k33bz/govee-outdoor-pegboard/models/cord_clips/cord_staple_13mm.stl

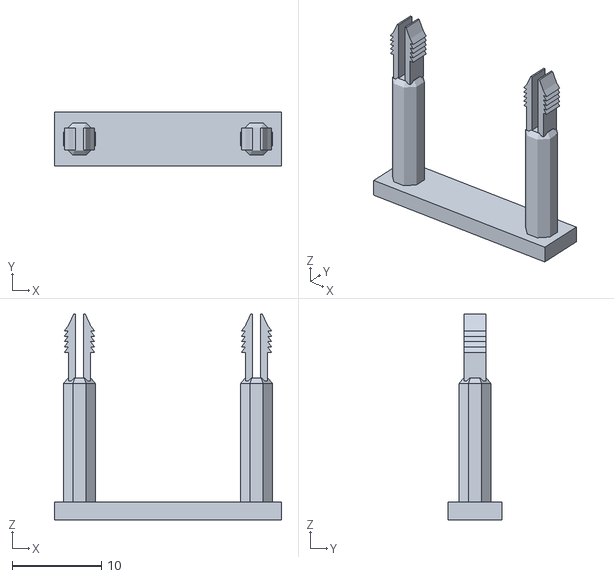
[picture p15: CAD file, 2026-08-23]
models/cord_clips/cord_staple_13mm.stl
25.5 x 6.00 x 23.1
