k33bz/govee-outdoor-pegboard/models/strip_mount/pitchspan_4.98mm.stl

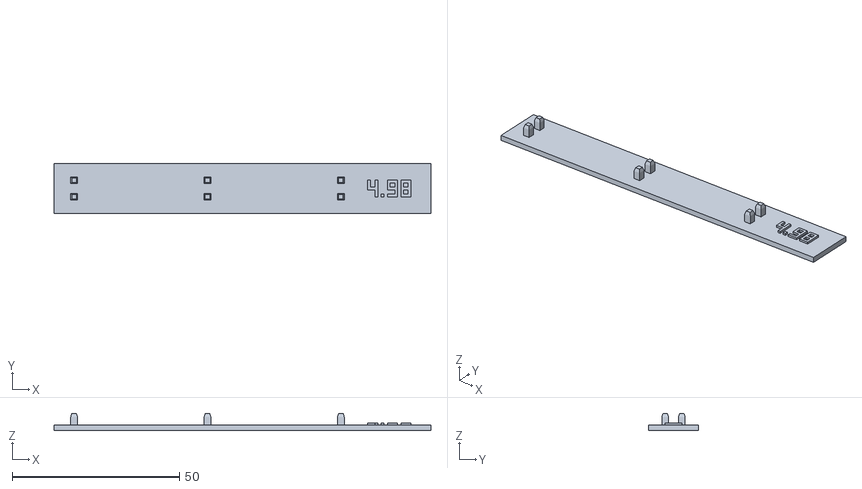
[picture p16: CAD file, 2026-08-21]
models/strip_mount/pitchspan_4.98mm.stl
112.6 x 15.0 x 5.10
