k33bz/govee-outdoor-pegboard/models/cord_clips/cord_staple_04mm.stl

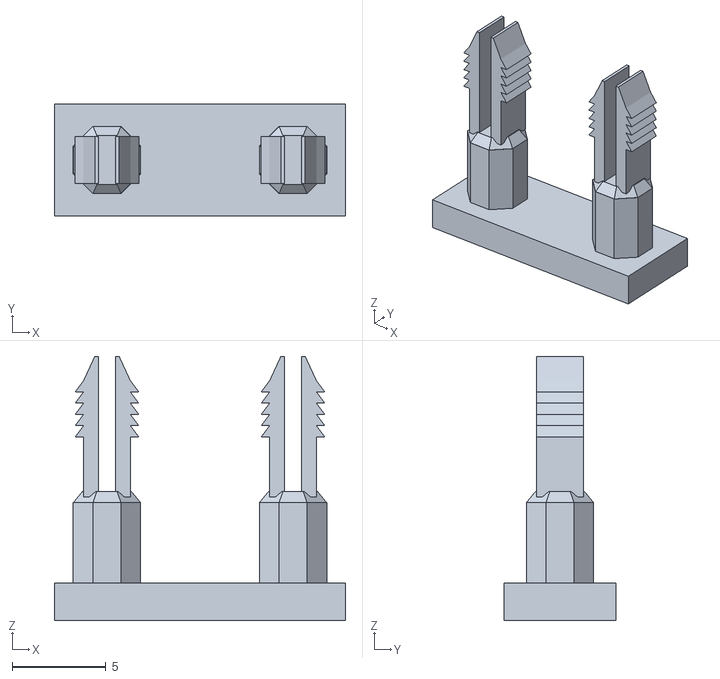
[picture p17: CAD file, 2026-08-23]
models/cord_clips/cord_staple_04mm.stl
15.5 x 6.00 x 14.1
