k33bz/govee-outdoor-pegboard/models/test_gauges/peg_size_gauge.stl

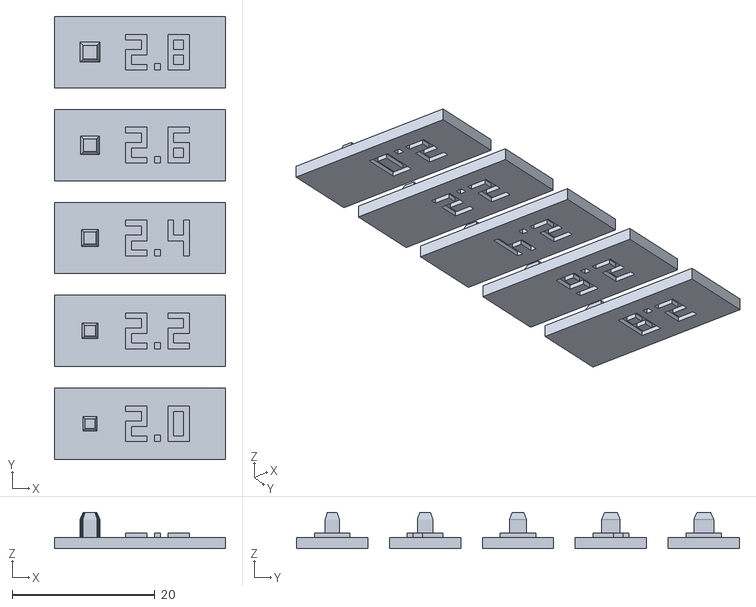
[picture p18: CAD file, 2026-08-20]
models/test_gauges/peg_size_gauge.stl
24.0 x 62.0 x 5.10
