k33bz/govee-outdoor-pegboard/models/cord_clips/cord_arch_10mm.stl

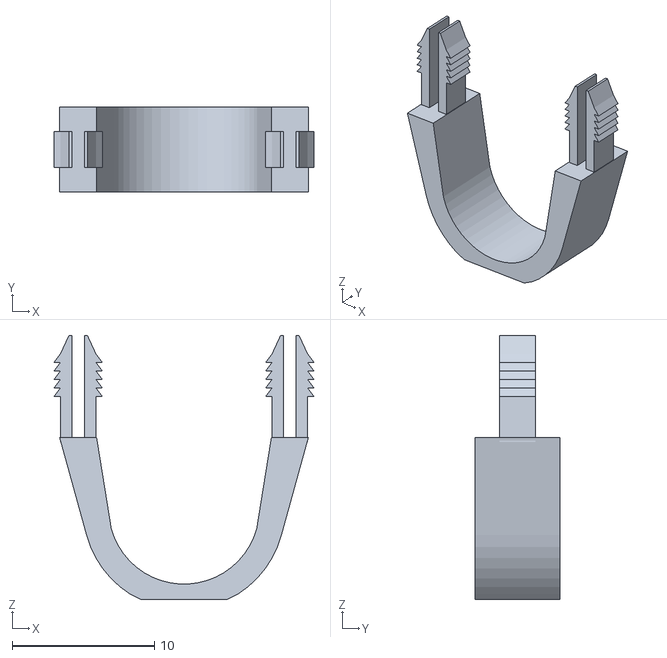
[picture p19: CAD file, 2026-08-23]
models/cord_clips/cord_arch_10mm.stl
18.3 x 6.00 x 18.6
