k33bz/govee-outdoor-pegboard/models/cord_clips/cord_arch_06mm.stl

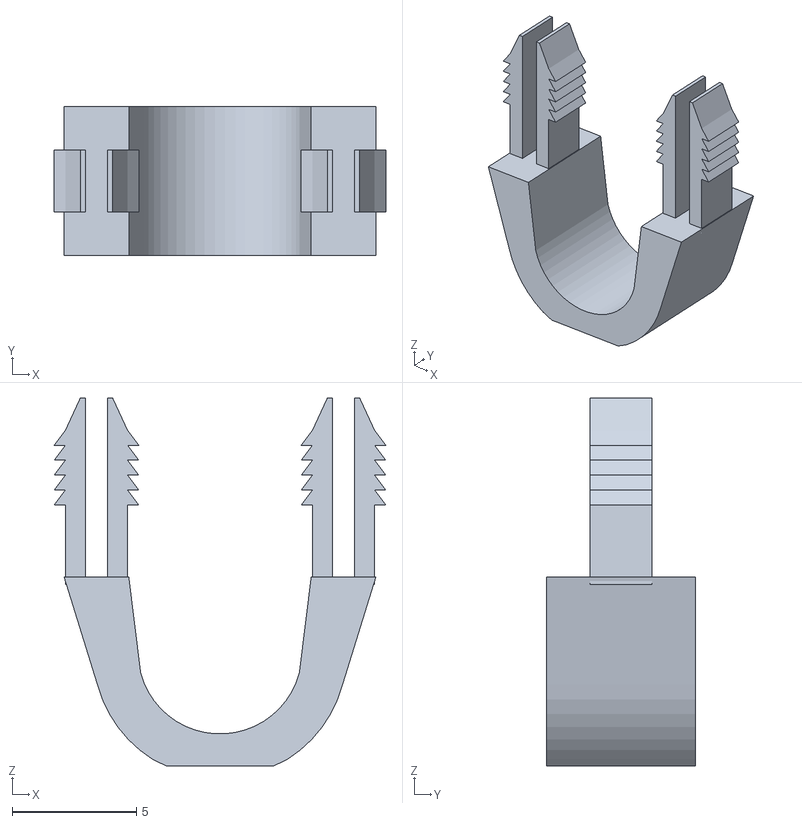
[picture p20: CAD file, 2026-08-23]
models/cord_clips/cord_arch_06mm.stl
13.3 x 6.00 x 14.8
