k33bz/govee-outdoor-pegboard/models/cord_clips/cord_arch_13mm.stl

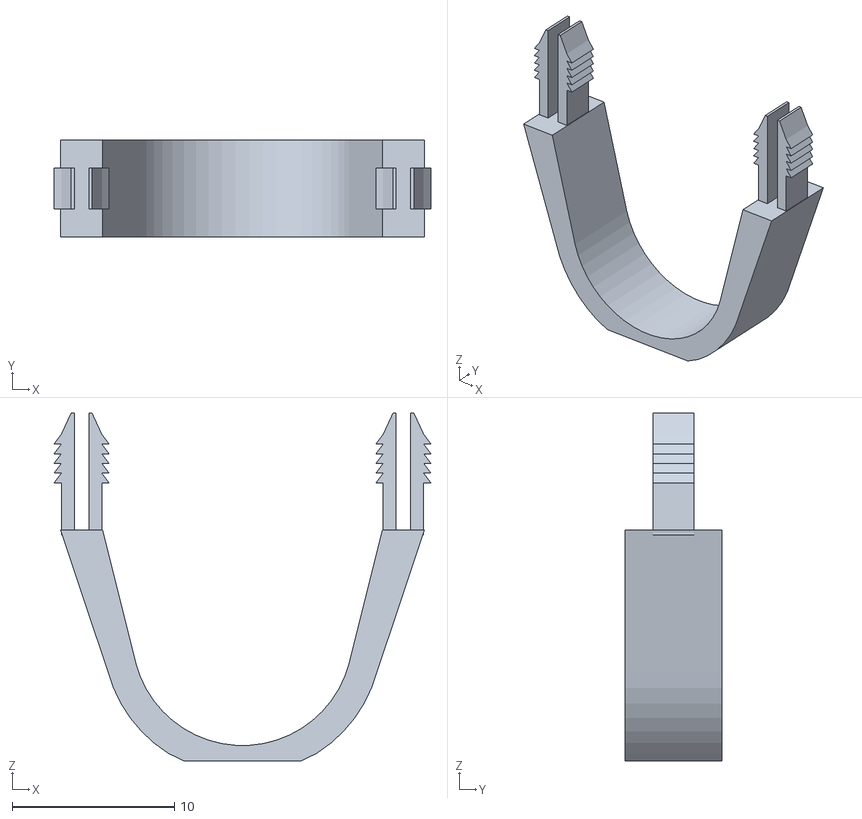
[picture p21: CAD file, 2026-08-23]
models/cord_clips/cord_arch_13mm.stl
23.3 x 6.00 x 21.4
