k33bz/govee-outdoor-pegboard/models/strip_mount/strip_hanger_test.stl

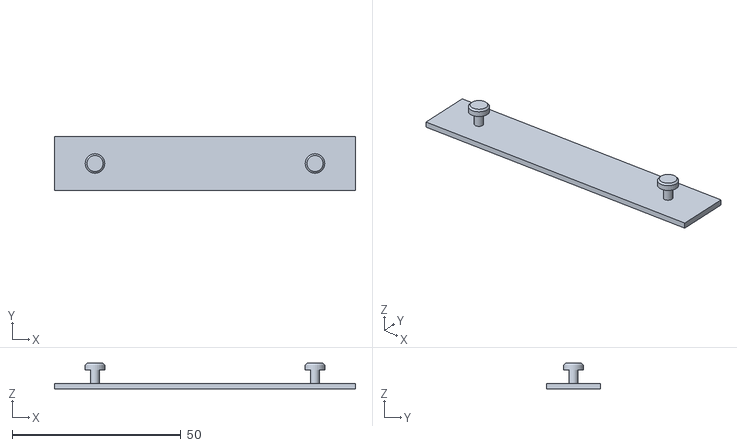
[picture p22: CAD file, 2026-08-21]
models/strip_mount/strip_hanger_test.stl
89.2 x 16.0 x 7.60
