k33bz/govee-outdoor-pegboard/models/cord_clips/cord_arch_08mm.stl

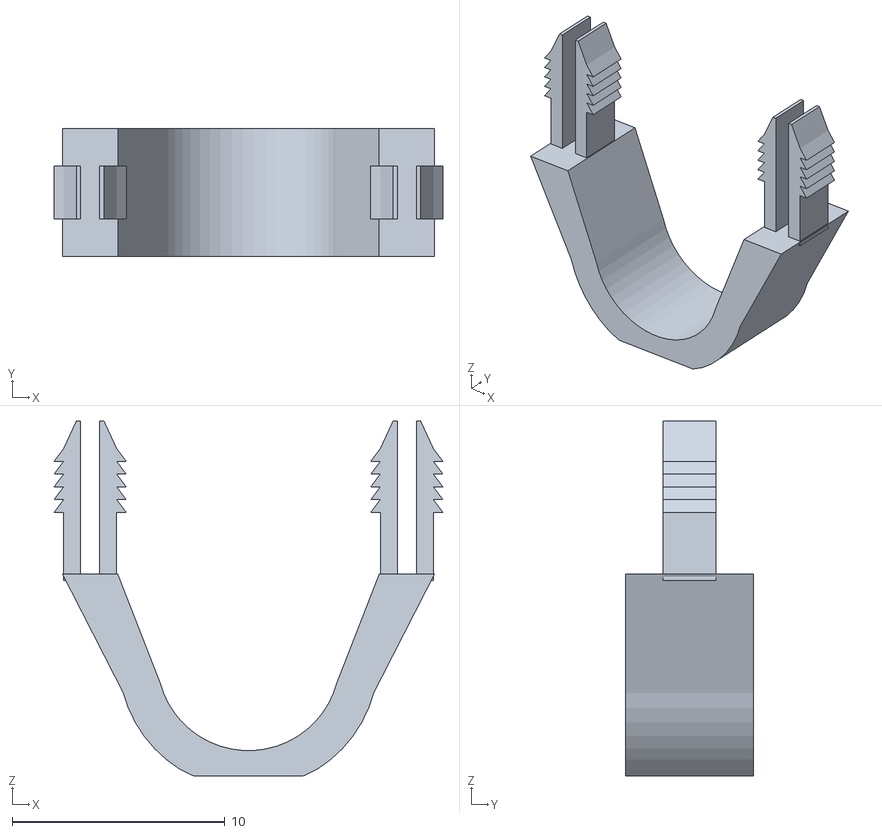
[picture p23: CAD file, 2026-08-23]
models/cord_clips/cord_arch_08mm.stl
18.3 x 6.00 x 16.7
