k33bz/govee-outdoor-pegboard/models/strip_mount/stud_gauge.stl

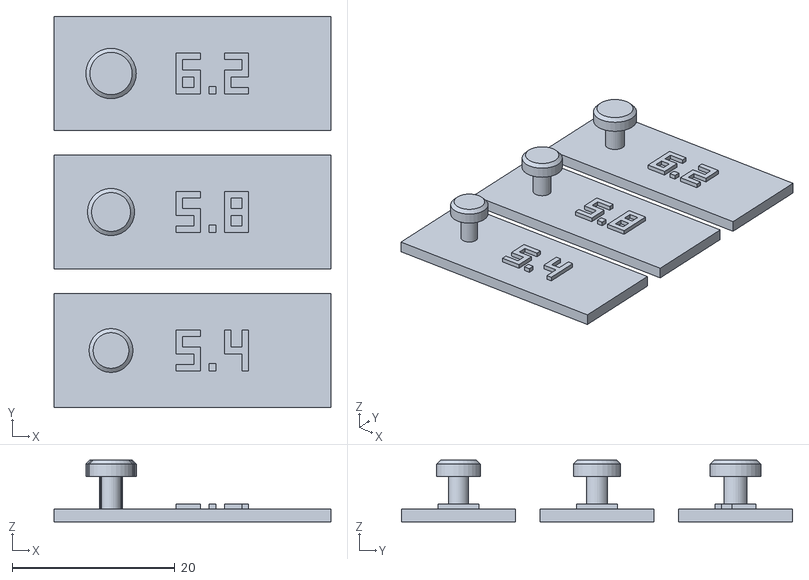
[picture p24: CAD file, 2026-08-21]
models/strip_mount/stud_gauge.stl
34.0 x 48.0 x 7.60
