k33bz/govee-outdoor-pegboard/models/cord_clips/cord_cradle_10mm.stl

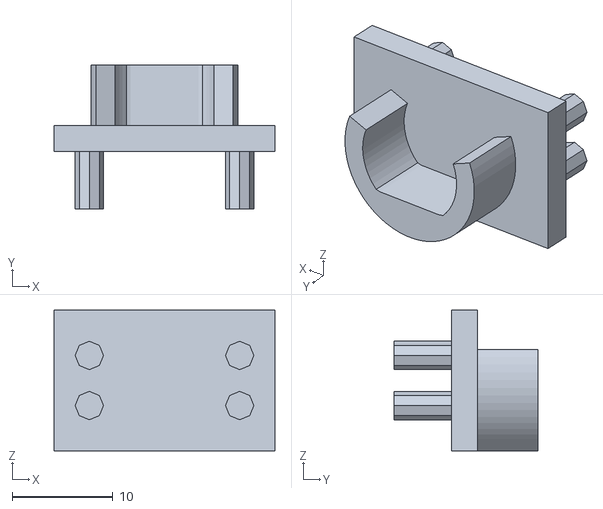
[picture p27: CAD file, 2026-08-23]
models/cord_clips/cord_cradle_10mm.stl
21.9 x 14.3 x 14.0
